AlaxLima/FiftyKeys/code/KeyLookupSwitch.h

#pragma once
#pragma message "Keybore is our new Keyboard!"

#include <Arduino.h>
#include <HID-Project.h>
#include <HID-Settings.h>

// -- KEYPRESSES GOES HERE --
inline void keyborePress(uint8_t keycode)
{
    switch (keycode)
    {
    case 0:
        Keyboard.press(KEY_RESERVED);
        break;
    case 1:
        Keyboard.press(KEY_ERROR_ROLLOVER);
        break;
    case 2:
        Keyboard.press(KEY_POST_FAIL);
        break;
    case 3:
        Keyboard.press(KEY_ERROR_UNDEFINED);
        break;
    case 4:
        Keyboard.press(KEY_A);
        break;
    case 5:
        Keyboard.press(KEY_B);
        break;
    case 6:
        Keyboard.press(KEY_C);
        break;
    case 7:
        Keyboard.press(KEY_D);
        break;
    case 8:
        Keyboard.press(KEY_E);
        break;
    case 9:
        Keyboard.press(KEY_F);
        break;
    case 10:
        Keyboard.press(KEY_G);
        break;
    case 11:
        Keyboard.press(KEY_H);
        break;
    case 12:
        Keyboard.press(KEY_I);
        break;
    case 13:
        Keyboard.press(KEY_J);
        break;
    case 14:
        Keyboard.press(KEY_K);
        break;
    case 15:
        Keyboard.press(KEY_L);
        break;
    case 16:
        Keyboard.press(KEY_M);
        break;
    case 17:
        Keyboard.press(KEY_N);
        break;
    case 18:
        Keyboard.press(KEY_O);
        break;
    case 19:
        Keyboard.press(KEY_P);
        break;
    case 20:
        Keyboard.press(KEY_Q);
        break;
    case 21:
        Keyboard.press(KEY_R);
        break;
    case 22:
        Keyboard.press(KEY_S);
        break;
    case 23:
        Keyboard.press(KEY_T);
        break;
    case 24:
        Keyboard.press(KEY_U);
        break;
    case 25:
        Keyboard.press(KEY_V);
        break;
    case 26:
        Keyboard.press(KEY_W);
        break;
    case 27:
        Keyboard.press(KEY_X);
        break;
    case 28:
        Keyboard.press(KEY_Y);
        break;
    case 29:
        Keyboard.press(KEY_Z);
        break;
    case 30:
        Keyboard.press(KEY_1);
        break;
    case 31:
        Keyboard.press(KEY_2);
        break;
    case 32:
        Keyboard.press(KEY_3);
        break;
    case 33:
        Keyboard.press(KEY_4);
        break;
    case 34:
        Keyboard.press(KEY_5);
        break;
    case 35:
        Keyboard.press(KEY_6);
        break;
    case 36:
        Keyboard.press(KEY_7);
        break;
    case 37:
        Keyboard.press(KEY_8);
        break;
    case 38:
        Keyboard.press(KEY_9);
        break;
    case 39:
        Keyboard.press(KEY_0);
        break;
    case 40:
        Keyboard.press(KEY_ENTER);
        break;
    case 41:
        Keyboard.press(KEY_ESC);
        break;
    case 42:
        Keyboard.press(KEY_BACKSPACE);
        break;
    case 43:
        Keyboard.press(KEY_TAB);
        break;
    case 44:
        Keyboard.press(KEY_SPACE);
        break;
    case 45:
        Keyboard.press(KEY_MINUS);
        break;
    case 46:
        Keyboard.press(KEY_EQUAL);
        break;
    case 47:
        Keyboard.press(KEY_LEFT_BRACE);
        break;
    case 48:
        Keyboard.press(KEY_RIGHT_BRACE);
        break;
    case 49:
        Keyboard.press(KEY_BACKSLASH);
        break;
    // Special case for LEFT ALT key interfering with code for Consumer MUTE
    case 50:
        Keyboard.press(KEY_LEFT_ALT);
        break;
    case 51:
        Keyboard.press(KEY_SEMICOLON);
        break;
    case 52:
        Keyboard.press(KEY_QUOTE);
        break;
    case 53:
        Keyboard.press(KEY_TILDE);
        break;
    case 54:
        Keyboard.press(KEY_COMMA);
        break;
    case 55:
        Keyboard.press(KEY_PERIOD);
        break;
    case 56:
        Keyboard.press(KEY_SLASH);
        break;
    case 57:
        Keyboard.press(KEY_CAPS_LOCK);
        break;
    case 58:
        Keyboard.press(KEY_F1);
        break;
    case 59:
        Keyboard.press(KEY_F2);
        break;
    case 60:
        Keyboard.press(KEY_F3);
        break;
    case 61:
        Keyboard.press(KEY_F4);
        break;
    case 62:
        Keyboard.press(KEY_F5);
        break;
    case 63:
        Keyboard.press(KEY_F6);
        break;
    case 64:
        Keyboard.press(KEY_F7);
        break;
    case 65:
        Keyboard.press(KEY_F8);
        break;
    case 66:
        Keyboard.press(KEY_F9);
        break;
    case 67:
        Keyboard.press(KEY_F10);
        break;
    case 68:
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
    case 249:
        Keyboard.release();
        break;
    case 250:
        Keyboard.release();
        break;
    case 251:
        Keyboard.release();
        break;
    case 252:
        Keyboard.release();
        break;
    case 253:
        Keyboard.release();
        break;
    case 254:
        Keyboard.release();
        break;
    */
    default:
        // Handle unknown key
        break;
    }
}

inline void consumeristPress(uint8_t keycode)
{
    switch (keycode)
    {
    case 48:
        Consumer.write(CONSUMER_POWER);
        Consumer.release(CONSUMER_POWER);
        break;
    case 49:
        Consumer.write(CONSUMER_SLEEP);
        Consumer.release(CONSUMER_SLEEP);
        break;
    case 111:
        Consumer.write(CONSUMER_BRIGHTNESS_UP);
        Consumer.release(CONSUMER_BRIGHTNESS_UP);
        break;
    case 112:
        Consumer.write(CONSUMER_BRIGHTNESS_DOWN);
        Consumer.release(CONSUMER_BRIGHTNESS_DOWN);
        break;
    case 178:
        Consumer.write(MEDIA_RECORD);
        Consumer.release(MEDIA_RECORD);
        break;
    case 179:
        Consumer.write(MEDIA_FAST_FORWARD);
        Consumer.release(MEDIA_FAST_FORWARD);
        break;
    case 180:
        Consumer.write(MEDIA_REWIND);
        Consumer.release(MEDIA_REWIND);
        break;
    case 181:
        Consumer.write(MEDIA_NEXT);
        Consumer.release(MEDIA_NEXT);
        break;
    case 182:
        Consumer.write(MEDIA_PREVIOUS);
        Consumer.release(MEDIA_PREVIOUS);
        break;
    case 183:
        Consumer.write(MEDIA_STOP);
        Consumer.release(MEDIA_STOP);
        break;
    case 185:
        Consumer.write(MEDIA_PAUSE);
        Consumer.release(MEDIA_PAUSE);
        break;
    case 205:
        Consumer.write(MEDIA_PLAY_PAUSE);
        Consumer.release(MEDIA_PLAY_PAUSE);
        break;
    case 226:
        // Consumer.press(MEDIA_VOLUME_MUTE);
        Consumer.write(MEDIA_VOLUME_MUTE);
        Consumer.release(MEDIA_VOLUME_MUTE);
        break;
    case 233:
        Consumer.write(MEDIA_VOLUME_UP);
        Consumer.release(MEDIA_VOLUME_UP);
        break;
    case 234:
        Consumer.write(MEDIA_VOLUME_DOWN);
        Consumer.release(MEDIA_VOLUME_DOWN);
        break;
    default:
        // Handle unknown key
        break;
    }
}

const uint8_t macroCount = 20; // Adjust depends on Memory limit

const uint8_t MacroMap[macroCount][20]{
    {1, KEY_RIGHT_CTRL, 1, KEY_RIGHT_SHIFT, 1, KEY_ESC, 0, KEY_ESC, 0, KEY_RIGHT_SHIFT, 0, KEY_RIGHT_CTRL},
    {1, KEY_LEFT_GUI, 1, KEY_TAB, 0, KEY_TAB, 0, KEY_LEFT_GUI},
    {1, KEY_LEFT_GUI, 1, KEY_L, 0, KEY_L, 0, KEY_LEFT_GUI},
    {1, KEY_LEFT_GUI, 1, KEY_A, 0, KEY_A, 0, KEY_LEFT_GUI},
    {1, KEY_RIGHT_CTRL, 1, KEY_RIGHT_GUI, 1, KEY_LEFT_ARROW, 0, KEY_LEFT_ARROW, 0, KEY_RIGHT_GUI, 0, KEY_RIGHT_CTRL},
    {1, KEY_RIGHT_CTRL, 1, KEY_RIGHT_GUI, 1, KEY_RIGHT_ARROW, 0, KEY_RIGHT_ARROW, 0, KEY_RIGHT_GUI, 0, KEY_RIGHT_CTRL}
};

// -- STATUS CHECK --
inline void keyboreStatus(bool upDown, uint8_t keycode)
{
    switch (upDown)
    {
    case 1:
        keyborePress(keycode);
        break;
    case 0:
        keyboreRelease(keycode);
        break;
    default:
        break;
    }
}

inline void consumeristStatus(bool upDown, uint8_t keycode)
{
    switch (upDown)
    {
    case 1:
        consumeristPress(keycode);
        break;
    case 0:
        break;
    default:
        break;
    }
}

const uint8_t consumerKeycodes[] = {
    111, 112,
    178, 179, 180, 181,
    182, 183, 185, 205,
    226, 233, 234};



// Identify whether use Consumer or Keyboard, as well as to press or release
inline void keyTypeLookup(bool upDown, uint8_t keycode)
{
    bool isConsumer = false;
    for (uint8_t c = 0; c < sizeof(consumerKeycodes) / sizeof(consumerKeycodes[0]); c++)
    {
        if (keycode == consumerKeycodes[c])
        {
            isConsumer = true;
            break;
        }
    }
    if (isConsumer)
    {
        consumeristStatus(upDown, keycode);
    }
    else
    {
        keyboreStatus(upDown, keycode);
    }
}

inline bool isMacroKeycode(uint8_t keycode)
{
    return (keycode >= 235 && keycode <= 254);
}

/*const uint8_t macroKeycodes[] = {
    235, 236, 237, 238, 239,
    240, 241, 242, 243, 244};
*/

inline void MacroRun(uint8_t macroCode)
{
    uint8_t MacroArrayRow;
    bool found = false;
    for (uint8_t c = 0; c < macroCount; c++)
    {
        switch (macroCode)
        {
        case 235:
            MacroArrayRow = 0;
            break;
        case 236:
            MacroArrayRow = 1;
            break;
        case 237:
            MacroArrayRow = 2;
            break;
        case 238:
            MacroArrayRow = 3;
            break;
        case 239:
            MacroArrayRow = 4;
            break;
        case 240:
            MacroArrayRow = 5;
            break;
        case 241:
            MacroArrayRow = 6;
            break;
        case 242:
            MacroArrayRow = 7;
            break;
        case 243:
            MacroArrayRow = 8;
            break;
        case 244:
            MacroArrayRow = 9;
            break;
        default:
            return;
        }
    }
    for (uint8_t m = 0; m < 100; m += 2)
    {
        keyTypeLookup(MacroMap[MacroArrayRow][m], MacroMap[MacroArrayRow][m + 1]);
        if (MacroMap[MacroArrayRow][m + 1] == 0)
        {
            break;
        }
    }
}
